TheoLephay/breathy/hardware/spice_sims/charger_darlington.asc

C1: cap; 10n
C2: cap; 1n
C3: cap; 1n
C4: cap; 0.1µ
C5: cap; 1n
D1: schottky; 1N5817
D2: schottky; 1N5817
Q1: pnp; BC557B
Q2: pnp; Q2SAR572D3
R1: res; 0R100
R2: res; 0.01R
R3: res; 10k
R4: res; 100k
R5: res; 23.8k
R6: res; 10k
R7: res; 1K
R8: res; 10k
R9: res; 1K
R10: res; 3K3
R11: res; 39K
R12: res; 5.1K
R13: res; 10k
R14: res; 1Meg
R15: res; 20
S1: sw
U1: opamp2; TLV9002
U3: TLV431
U4: TLV431
U5: opamp2; TLV9002
V1: voltage; 5
V2: voltage; 0.2
V3: voltage; 4
V4: voltage; 4.2
V5: voltage; PULSE(0 2 20m 10n 10n 20m 40m)
Named nets: 0, 5V
.tran 0 500m 0 uic
.include components/tlv9002.lib
.lib components/2sar572d3_ltspice.lib
.model SW SW(Ron=0.001 Roff=10Meg Vt=1 Vh=-0.4)
to simulate variable MCU load without battery
